RoboDurden/Esp32_20A_80V_dcdc/Blender/JogDial.jpg

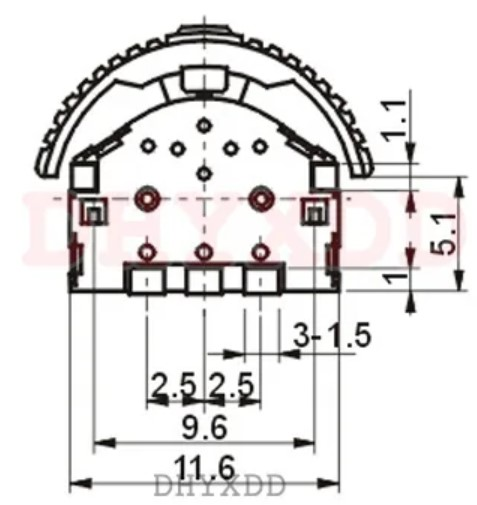
Blender/JogDial.jpg
