RoboDurden/Esp32_20A_80V_dcdc/Blender/tft 1,8inch with touch.jpg

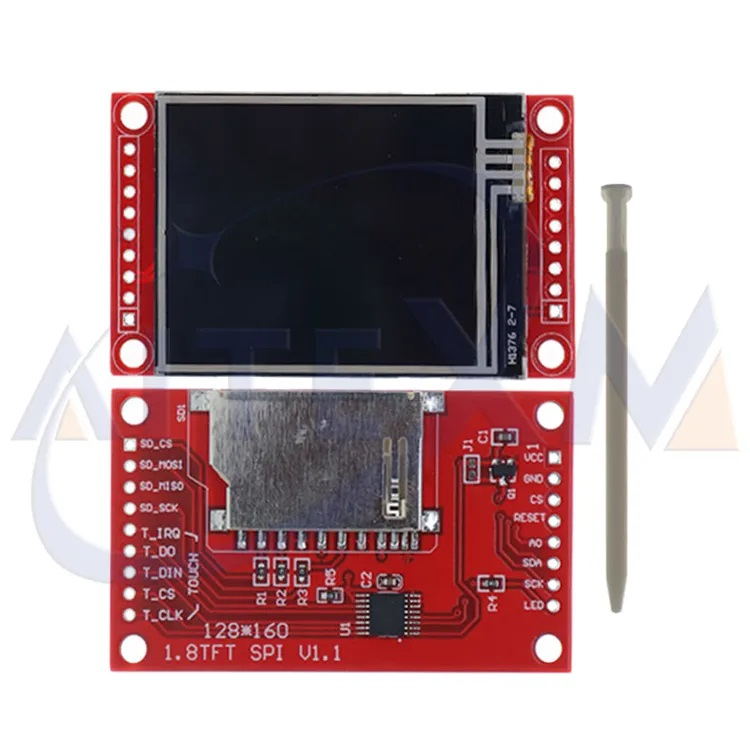
Blender/tft 1,8inch with touch.jpg
