RoboDurden/Esp32_20A_80V_dcdc/docs/20A zwischenplatine 2.jpg

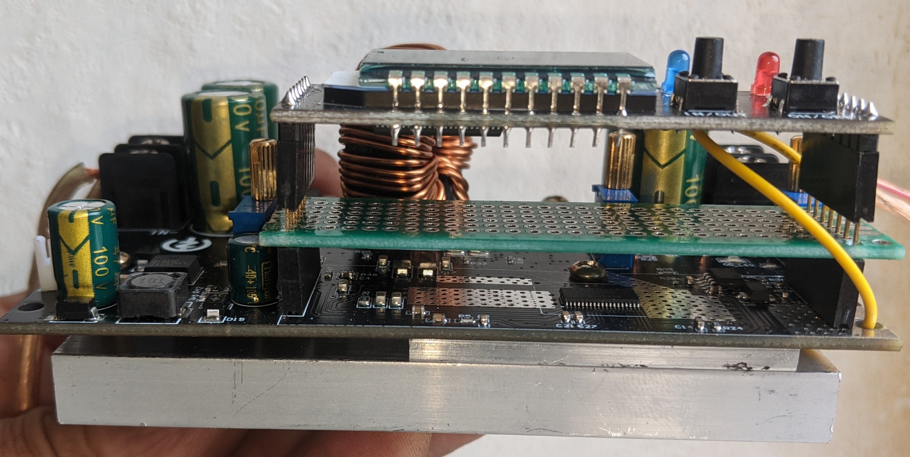
docs/20A zwischenplatine 2.jpg
