RoboDurden/Esp32_20A_80V_dcdc/docs/AliExpress dcdc/Sc2e96b0cd979476e8be64ace0491f06ad.webp

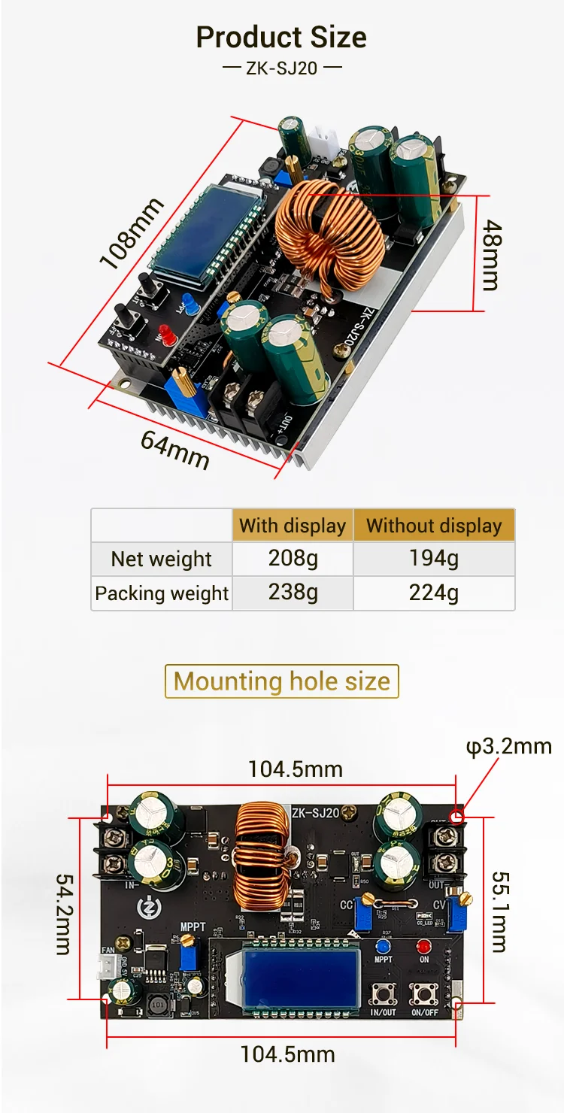
docs/AliExpress dcdc/Sc2e96b0cd979476e8be64ace0491f06ad.webp
