RoboDurden/Esp32_20A_80V_dcdc/docs/AliExpress dcdc/Sd0eb987eaa35409baaf90c5f975168d88.webp

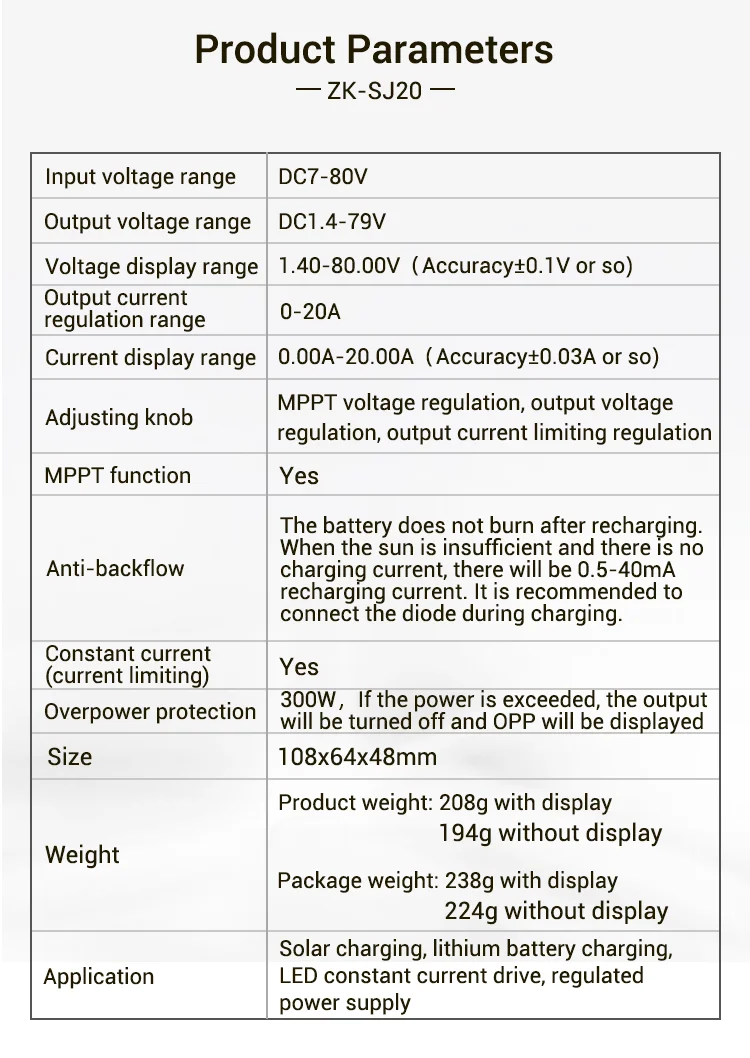
docs/AliExpress dcdc/Sd0eb987eaa35409baaf90c5f975168d88.webp
