RoboDurden/Esp32_20A_80V_dcdc/docs/Reverse Current.jpg

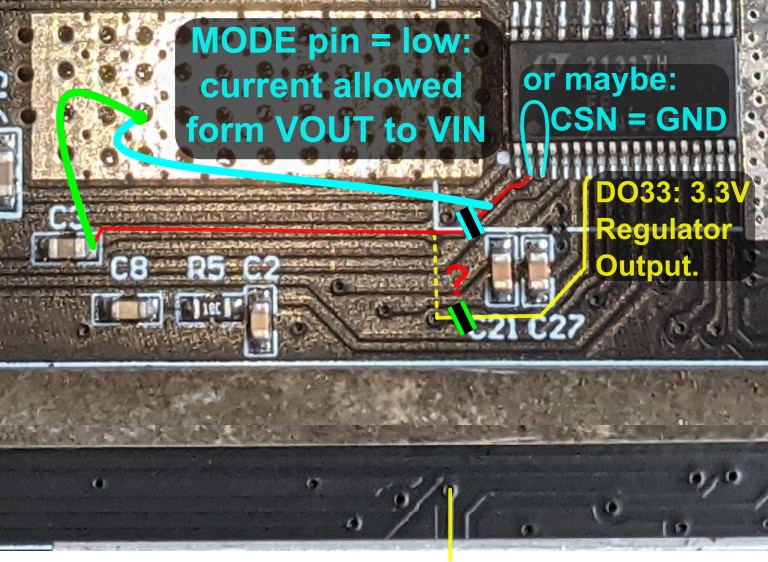
docs/Reverse Current.jpg
