RoboDurden/Esp32_20A_80V_dcdc/readme_img/3d3s.jpg

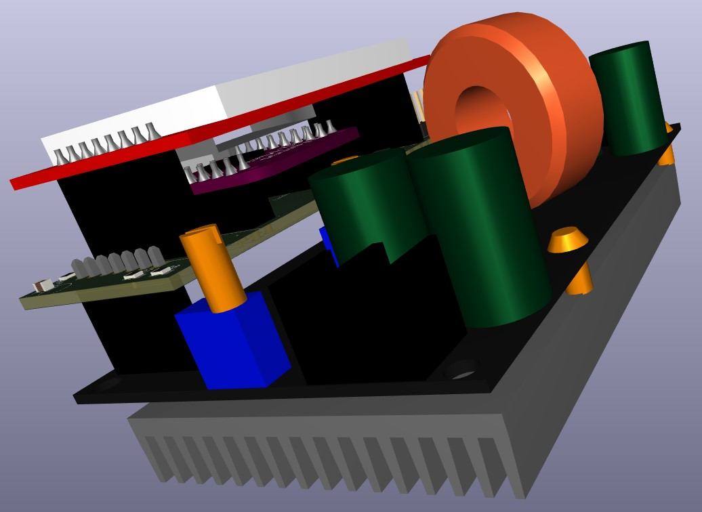
readme_img/3d3s.jpg
