RoboDurden/Esp32_20A_80V_dcdc/Blender/20A 80V step-up-down.jpg

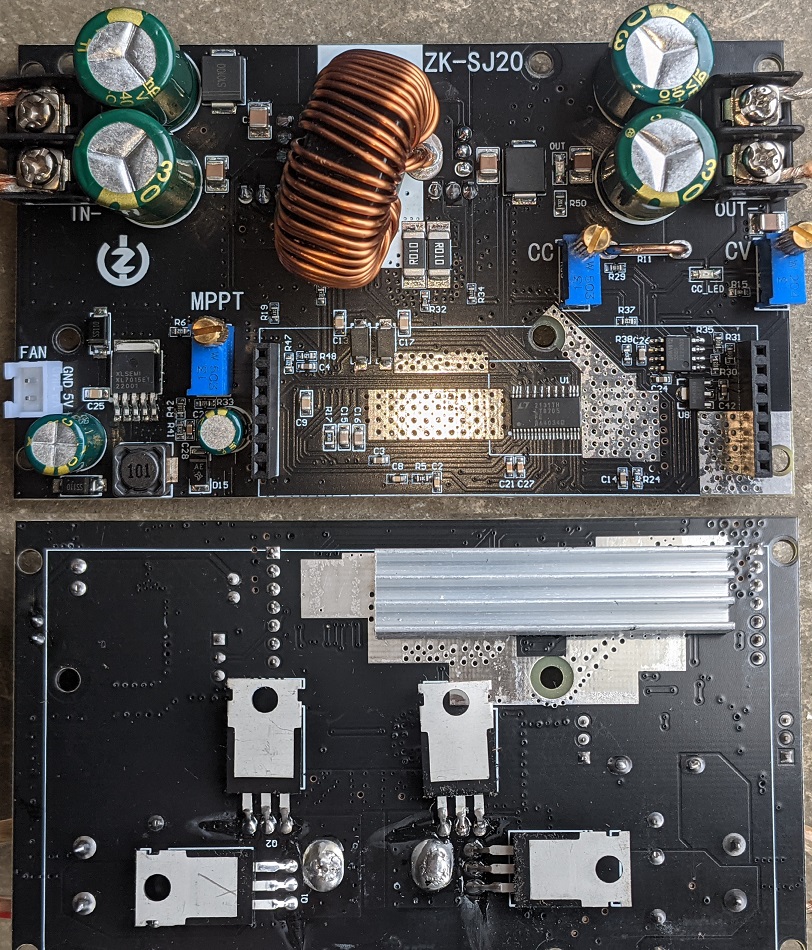
Blender/20A 80V step-up-down.jpg
