RoboDurden/Esp32_20A_80V_dcdc/Arduino/Mppt_LT8705/Dialog_plain_32.h

// Created by http://oleddisplay.squix.ch/ Consider a donation
// In case of problems make sure that you are using the font file with the correct version!
const uint8_t Dialog_plain_32[] PROGMEM = {
  0x20, // Width: 32
  0x26, // Height: 38
  0x20, // First Char: 32
  0xE0, // Numbers of Chars: 224

  // Jump Table:
  0xFF, 0xFF, 0x00, 0x0A,  // 32:65535
  0x00, 0x00, 0x27, 0x0D,  // 33:0
  0x00, 0x27, 0x39, 0x0F,  // 34:39
  0x00, 0x60, 0x75, 0x1B,  // 35:96
  0x00, 0xD5, 0x59, 0x14,  // 36:213
  0x01, 0x2E, 0x90, 0x1E,  // 37:302
  0x01, 0xBE, 0x77, 0x19,  // 38:446
  0x02, 0x35, 0x1B, 0x09,  // 39:565
  0x02, 0x50, 0x32, 0x0C,  // 40:592
  0x02, 0x82, 0x31, 0x0C,  // 41:642
  0x02, 0xB3, 0x49, 0x10,  // 42:691
  0x02, 0xFC, 0x76, 0x1B,  // 43:764
  0x03, 0x72, 0x22, 0x0A,  // 44:882
  0x03, 0x94, 0x30, 0x0C,  // 45:916
  0x03, 0xC4, 0x22, 0x0A,  // 46:964
  0x03, 0xE6, 0x34, 0x0B,  // 47:998
  0x04, 0x1A, 0x58, 0x14,  // 48:1050
  0x04, 0x72, 0x54, 0x14,  // 49:1138
  0x04, 0xC6, 0x54, 0x14,  // 50:1222
  0x05, 0x1A, 0x54, 0x14,  // 51:1306
  0x05, 0x6E, 0x5E, 0x14,  // 52:1390
  0x05, 0xCC, 0x54, 0x14,  // 53:1484
  0x06, 0x20, 0x59, 0x14,  // 54:1568
  0x06, 0x79, 0x52, 0x14,  // 55:1657
  0x06, 0xCB, 0x59, 0x14,  // 56:1739
  0x07, 0x24, 0x58, 0x14,  // 57:1828
  0x07, 0x7C, 0x22, 0x0B,  // 58:1916
  0x07, 0x9E, 0x22, 0x0B,  // 59:1950
  0x07, 0xC0, 0x72, 0x1B,  // 60:1984
  0x08, 0x32, 0x72, 0x1B,  // 61:2098
  0x08, 0xA4, 0x71, 0x1B,  // 62:2212
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
  0x00,0x00,0x00,0x00,0x00,0x00,0x00,0x00,0x00,0x00,0x00,0x00,0x00,0x00,0x00,0x80,0xFF,0xFF,0x3F,0x00,0x80,0xFF,0xFF,0x3F,0x00,0x80,0xFF,0xFF,0x3F,0x00,0x00,0x00,0x07,0x00,0x00,0x00,0x00,0x07,0x00,0x00,0x00,0x00,0x07,0x00,0x00,0x00,0x00,0x07,0x00,0x00,0x00,0x00,0x07,0x00,0x00,0x00,0x00,0x07,0x00,0x00,0x00,0x00,0x07,0x00,0x00,0x00,0x00,0x07,0x00,0x00,0x00,0x00,0x07,0x00,0x00,0x00,0x00,0x07,0x00,0x00,0x00,0x00,0x07,0x00,0x00,0x00,0x00,0x07,0x00,0x00,0x80,0xFF,0xFF,0x3F,0x00,0x80,0xFF,0xFF,0x3F,0x00,0x80,0xFF,0xFF,0x3F,  // 72
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
};
